jernst/stackie-shelfie/peg05x1_A1.scad

//
// Stacky Half-Peg for Board "A" 8 cm, extends through board
//
// (C) 2019 Johannes Ernst.
// License: see package.
//

include <lib/peg_A.scad>

peg_A( 0.5, 1, 1, hole_h = 0 );
