jernst/stackie-shelfie/xpeg4x1_A8t.scad

//
// Stacky X-Peg for Board "A" 8cm tall, 4cm wide, extends through board
//
// (C) 2019 Johannes Ernst.
// License: see package.
//

include <lib/xpeg_A.scad>

xpeg_At( 4, 1, 8 );
